skeatz/FabFTDI/images/fabftdi-ch340g_outline.png

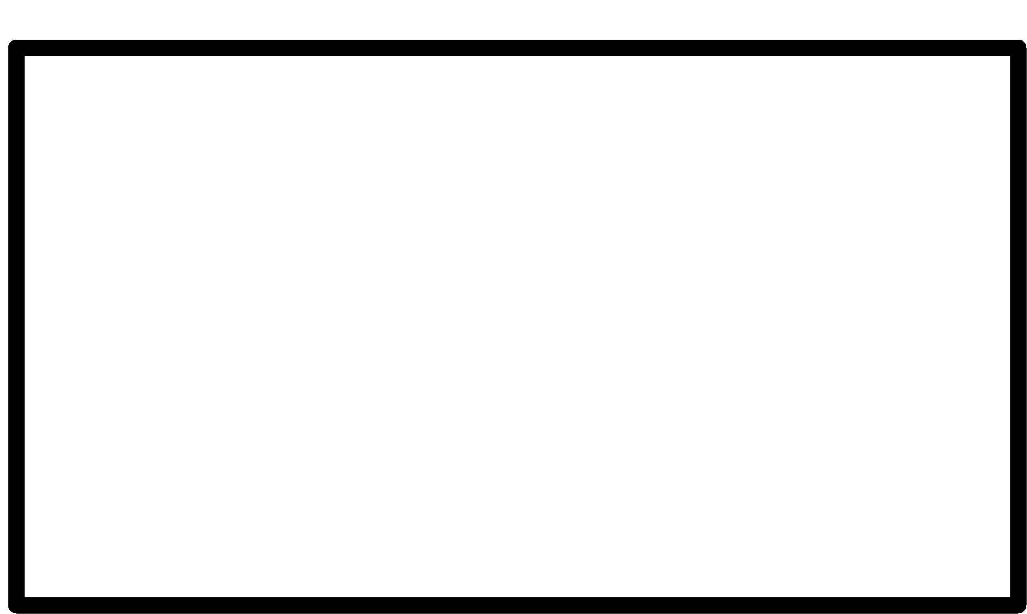
images/fabftdi-ch340g_outline.png
