skeatz/FabFTDI/images/fabftdi-ch340g_traces.png

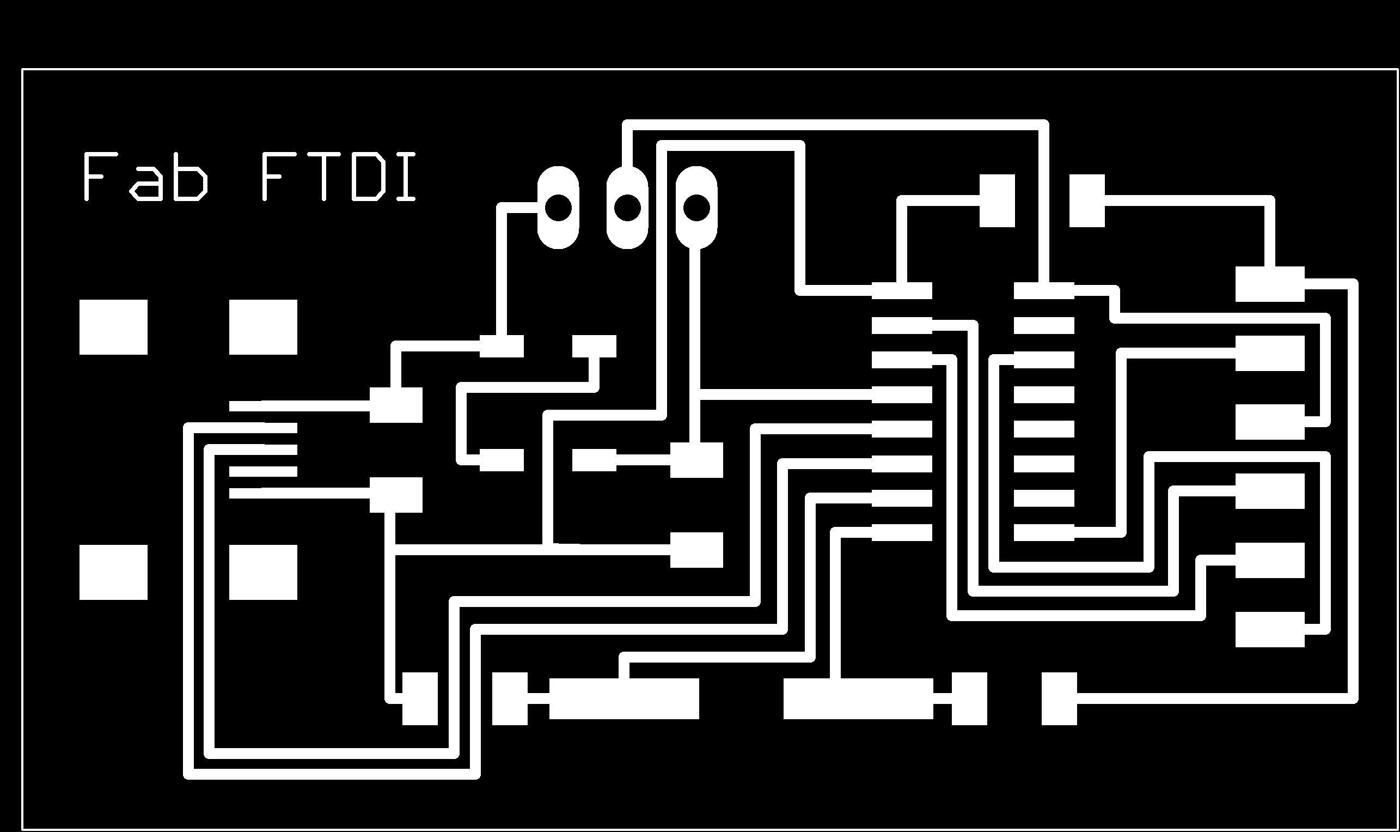
images/fabftdi-ch340g_traces.png
