skeatz/FabFTDI/images/fabftdi-t45x_01.png

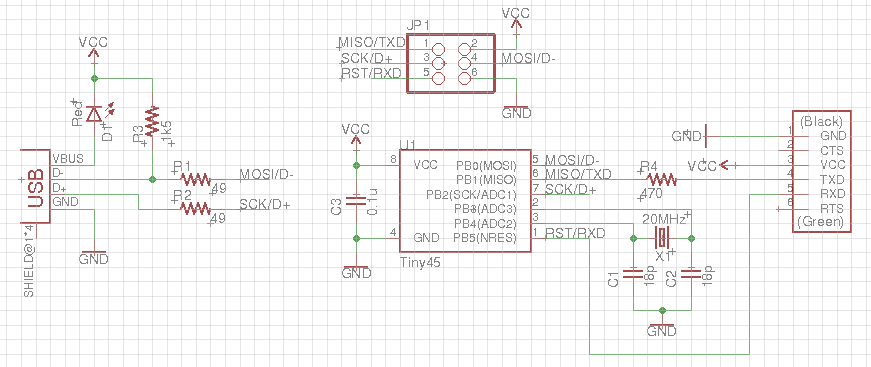
images/fabftdi-t45x_01.png
