skeatz/FabFTDI/images/fabftdi-t45x_03.png

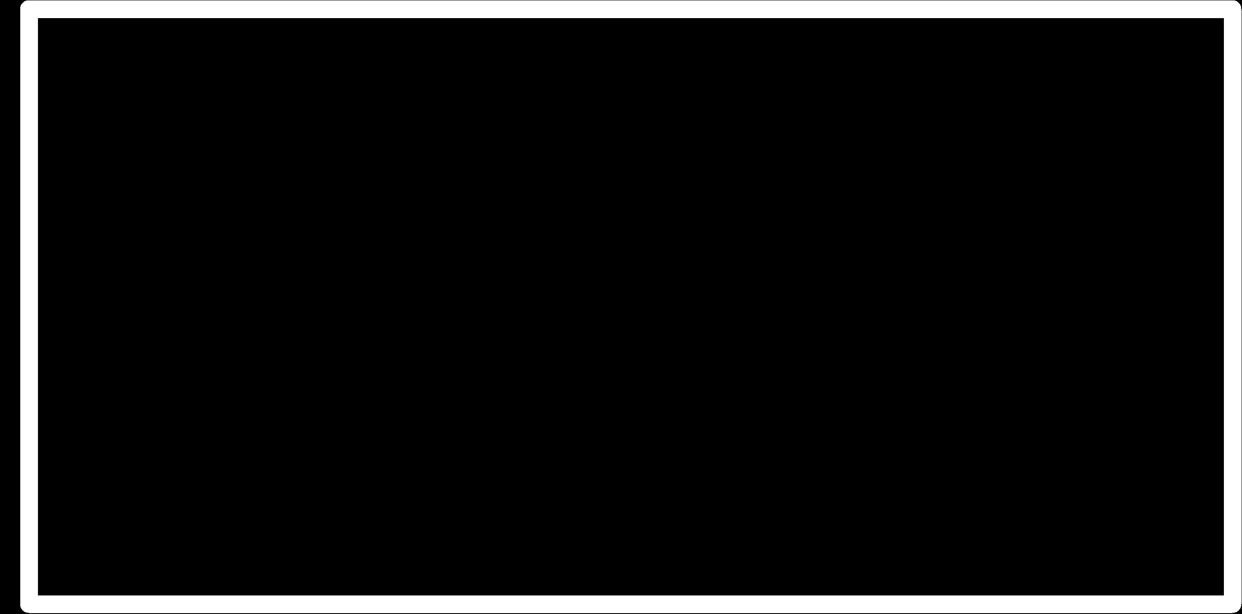
images/fabftdi-t45x_03.png
