skeatz/FabFTDI/images/fabftdi-t2313_03.png

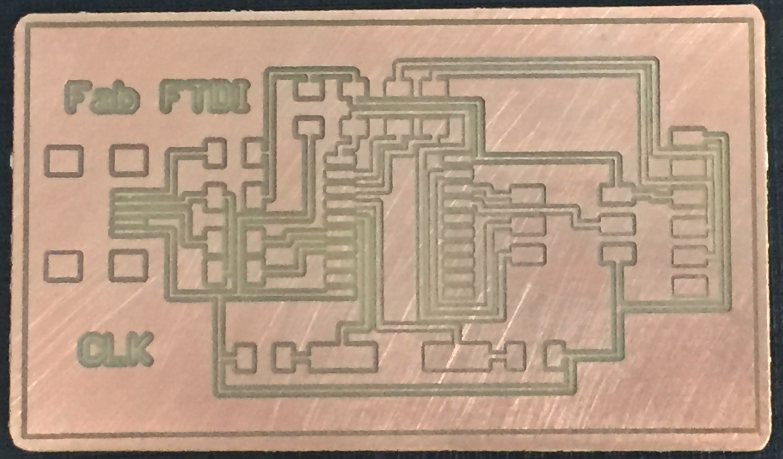
images/fabftdi-t2313_03.png
